pilnikov/WeatherStation/extras/Controllers_sensors/shematic in png/control.png

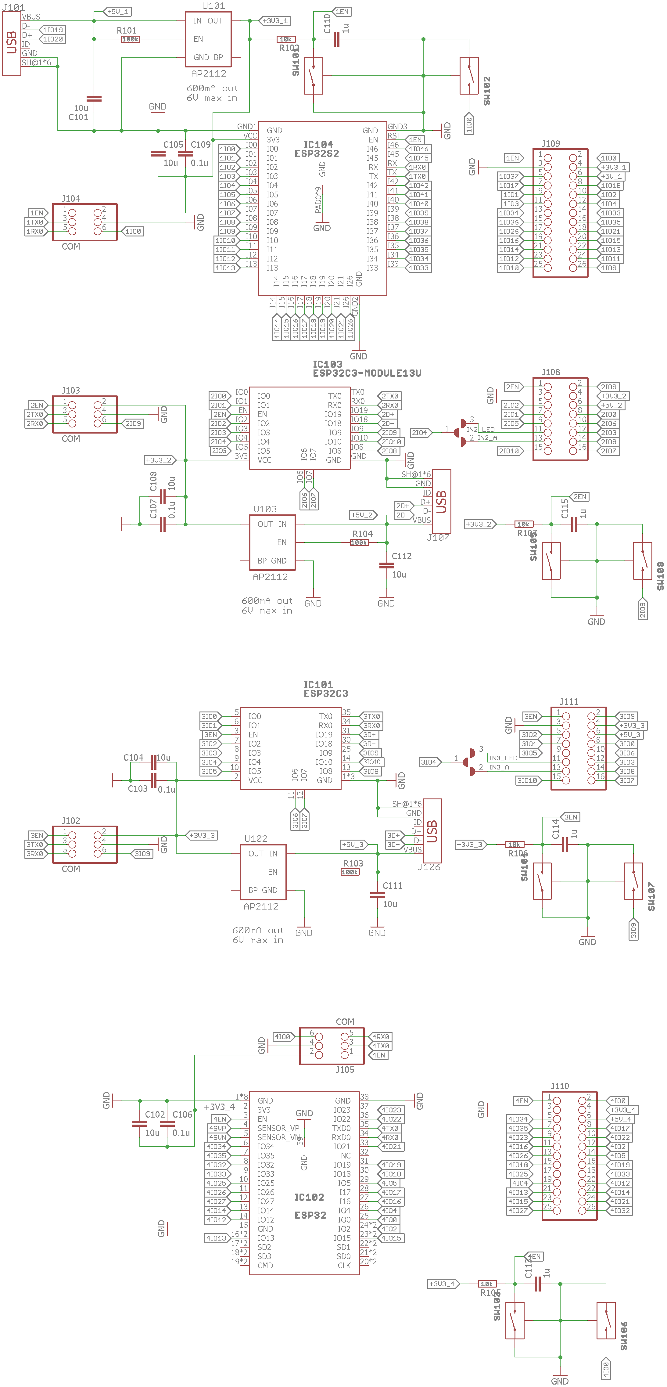
extras/Controllers_sensors/shematic in png/control.png
