pilnikov/WeatherStation/extras/Controllers_sensors/shematic in png/sensor.png

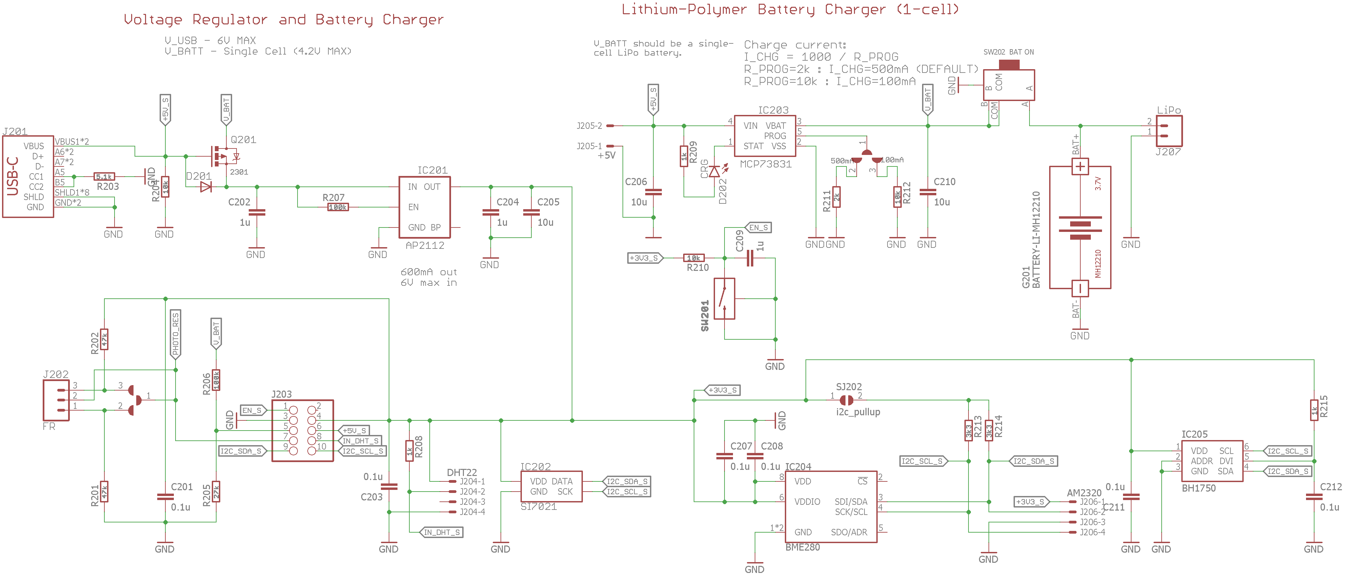
extras/Controllers_sensors/shematic in png/sensor.png
