pilnikov/WeatherStation/extras/Controllers_sensors/shematic in png/usb.png

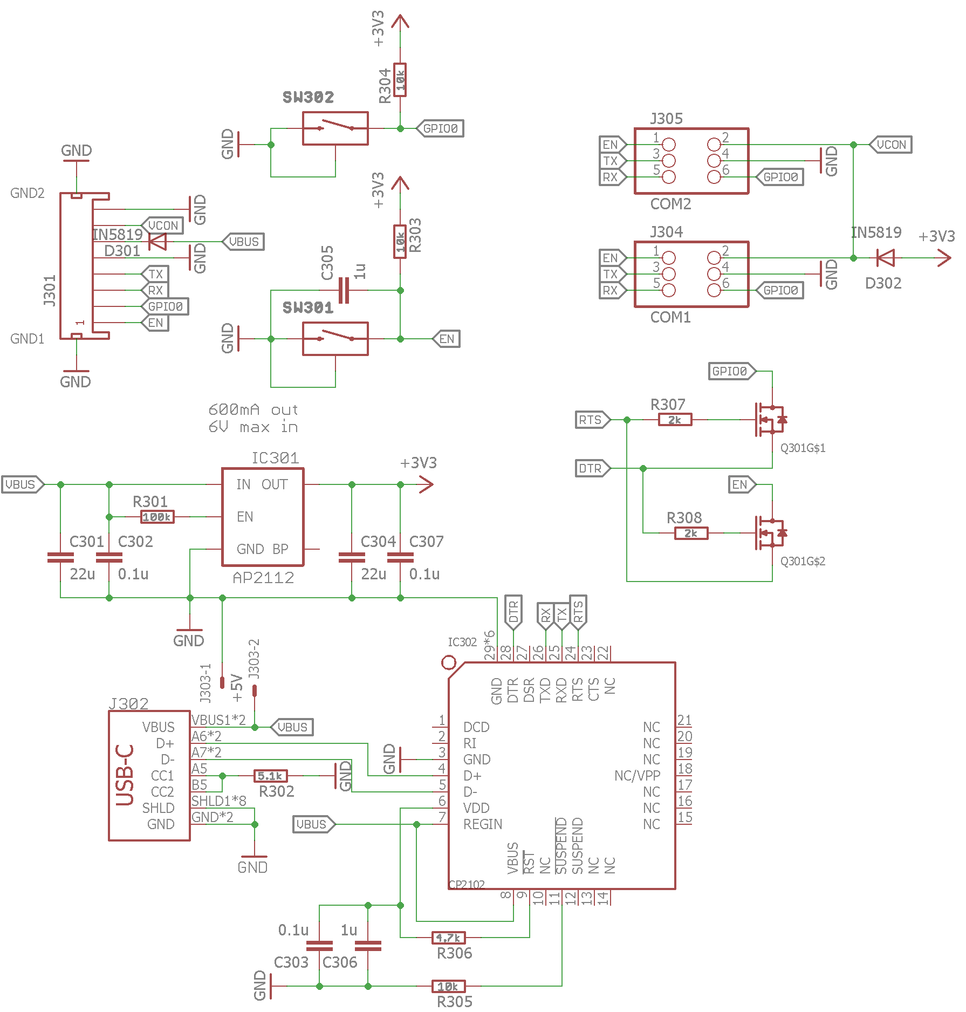
extras/Controllers_sensors/shematic in png/usb.png
