pilnikov/WeatherStation/extras/esp32_hub75/shematic in png/main.png

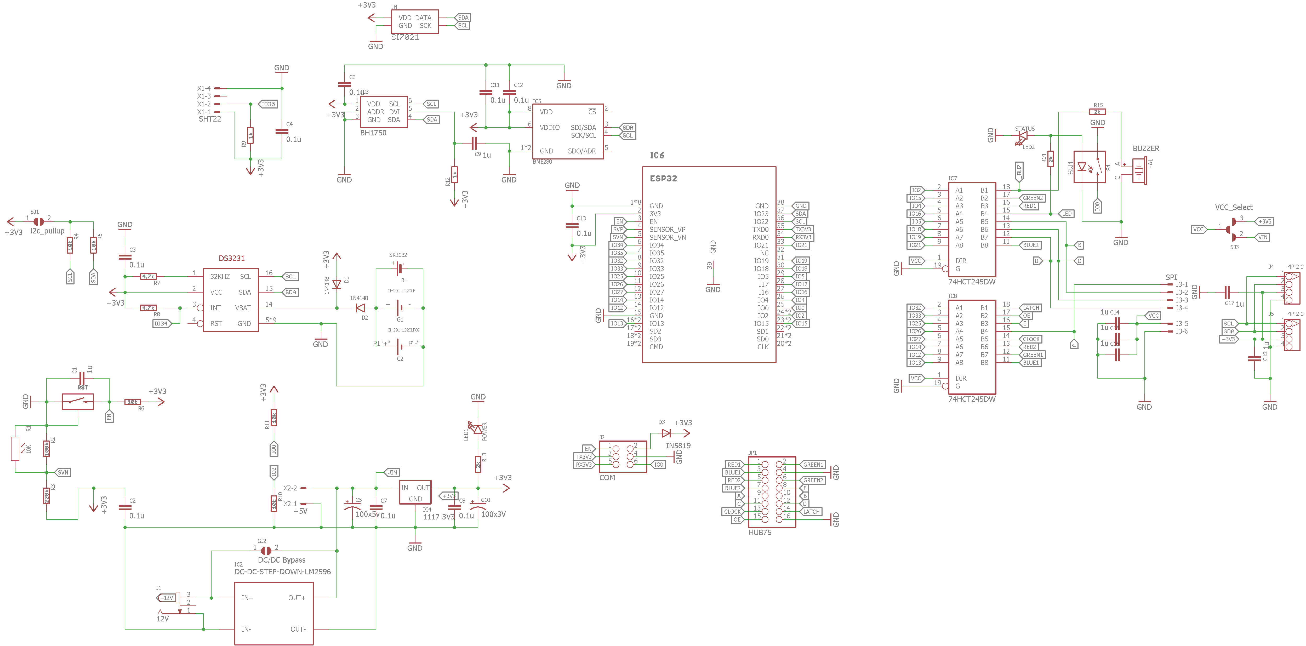
extras/esp32_hub75/shematic in png/main.png
