pilnikov/WeatherStation/extras/Main_board/shematic in png/MAIN.png

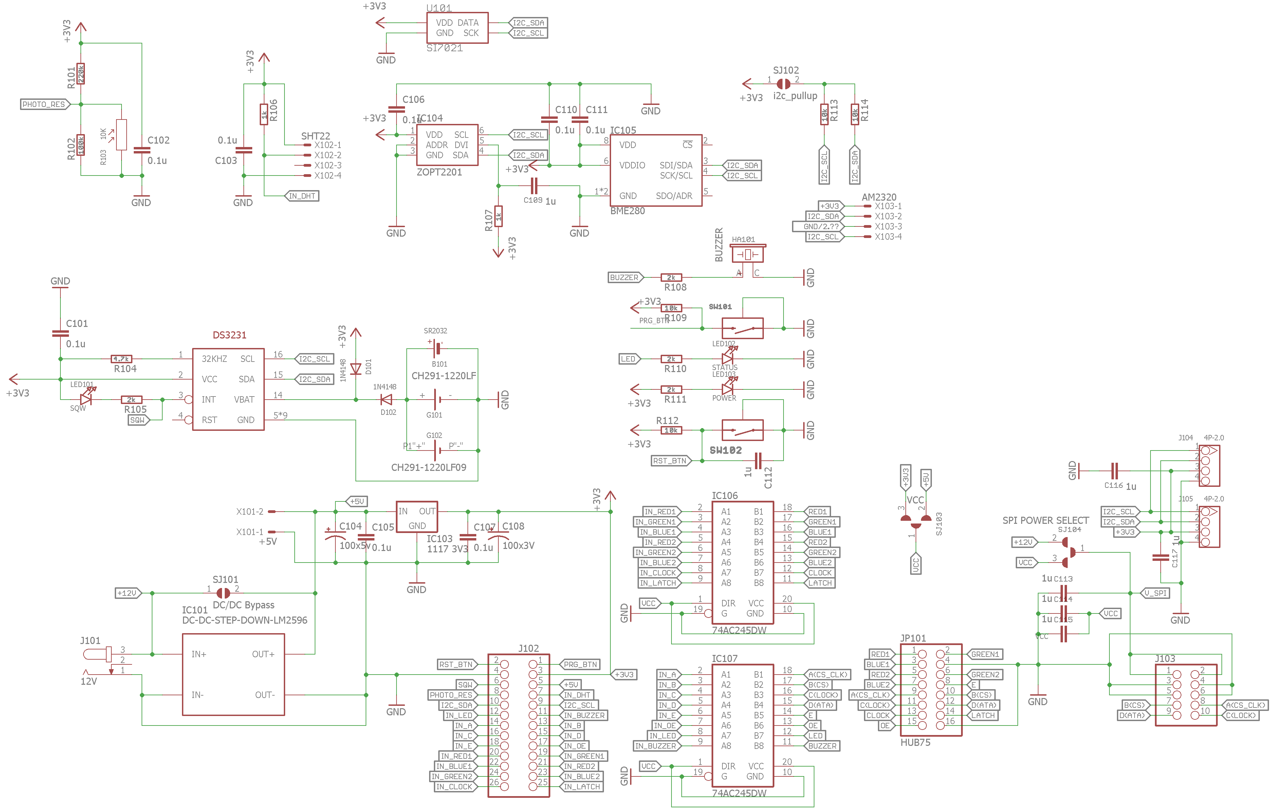
extras/Main_board/shematic in png/MAIN.png
