pilnikov/WeatherStation/extras/Main_board/shematic in png/wifi com.png

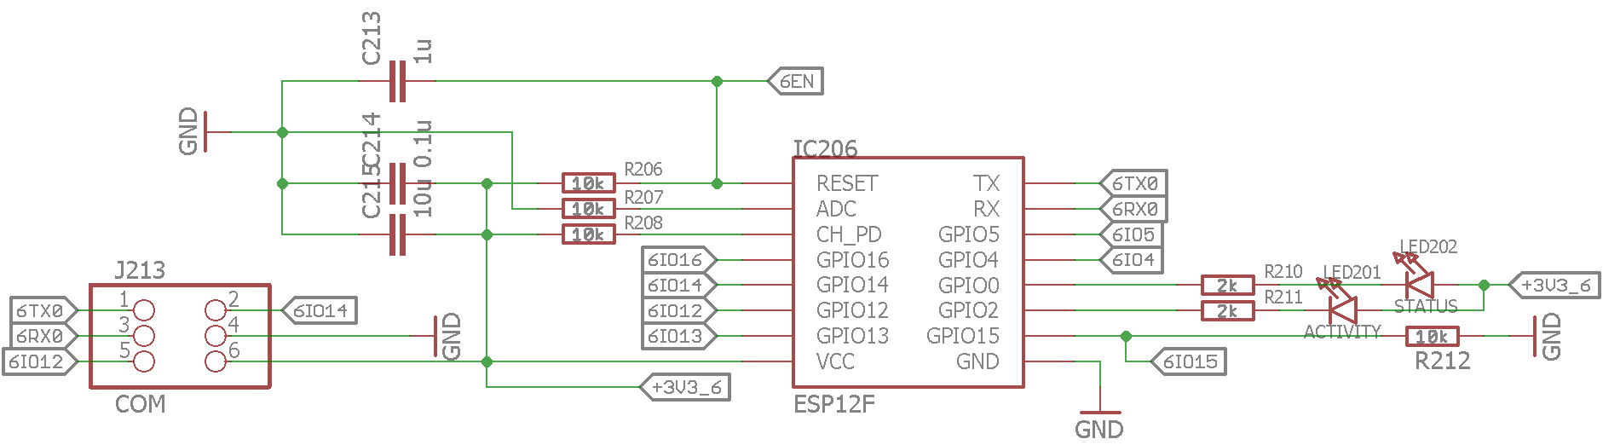
extras/Main_board/shematic in png/wifi com.png
