pilnikov/WeatherStation/extras/max7219_16x32/shematic in png/als318.png

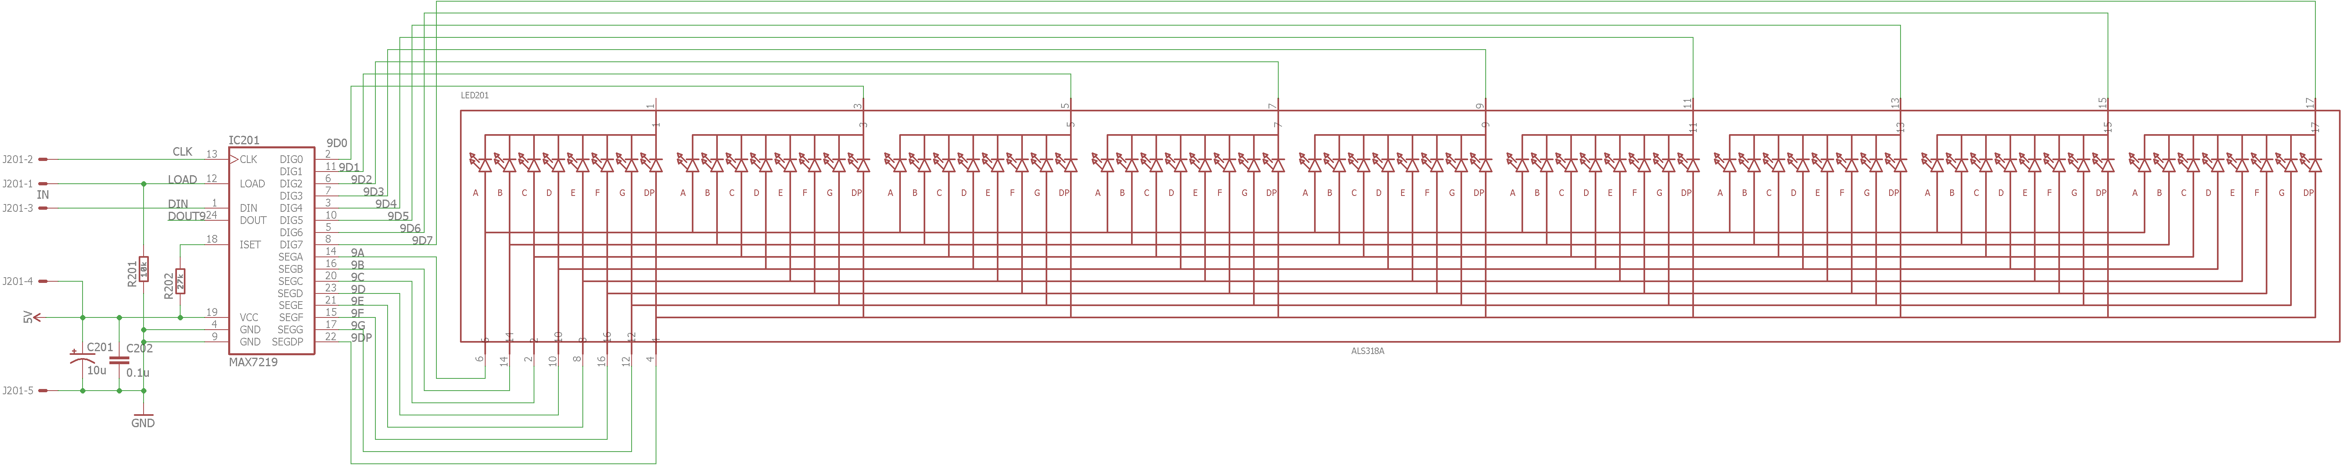
extras/max7219_16x32/shematic in png/als318.png
