pilnikov/WeatherStation/extras/max7219_16x32/shematic in png/main.png

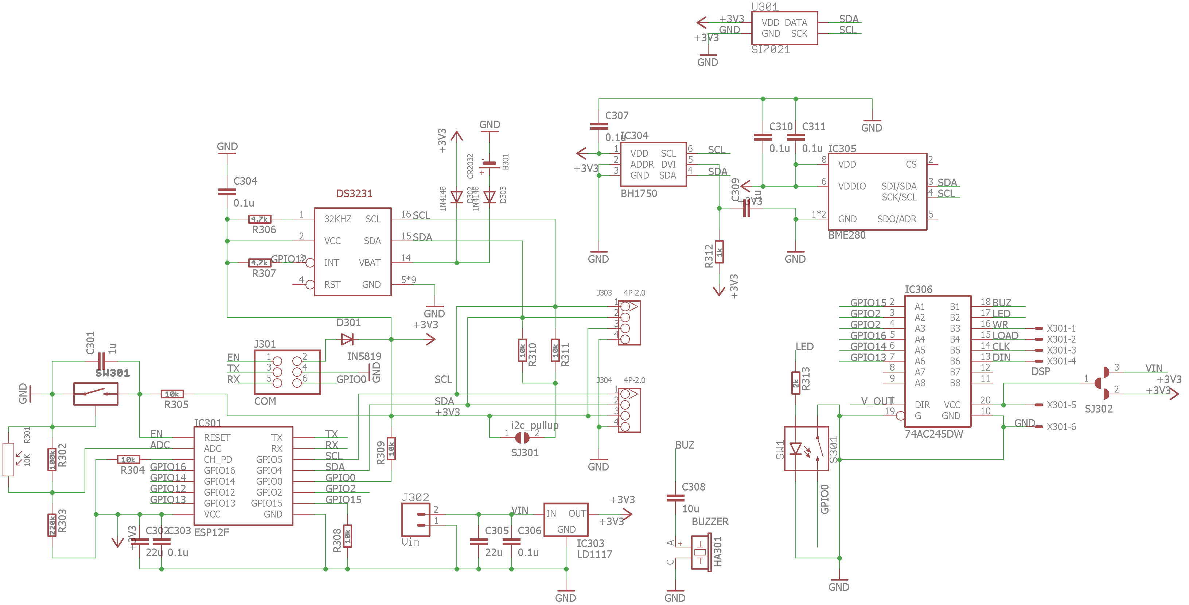
extras/max7219_16x32/shematic in png/main.png
