pilnikov/WeatherStation/extras/max7219_16x32/shematic in png/matrix.png

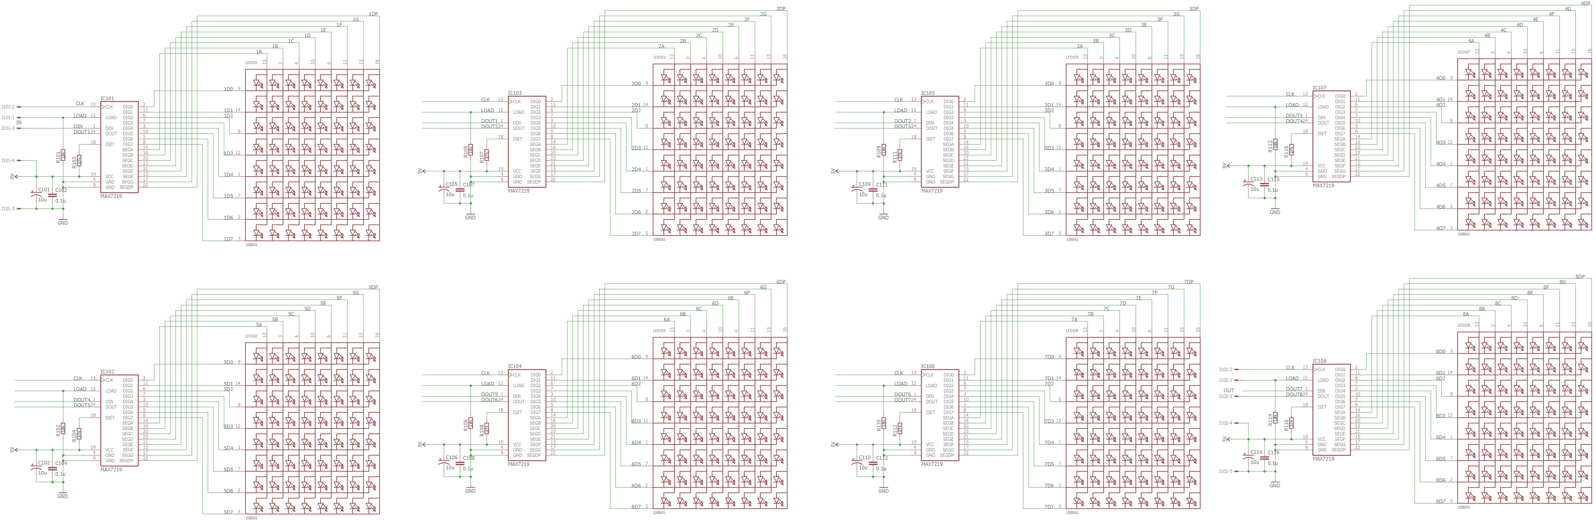
extras/max7219_16x32/shematic in png/matrix.png
