pilnikov/WeatherStation/extras/max7219_16x32/shematic in png/usb.png

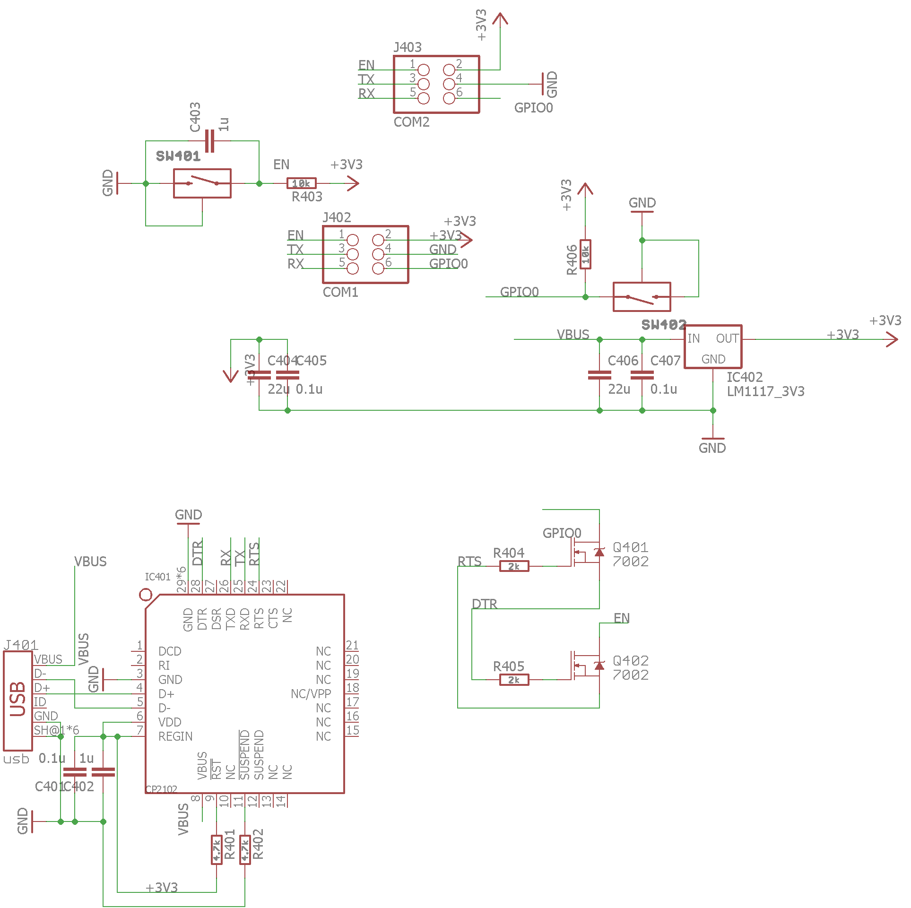
extras/max7219_16x32/shematic in png/usb.png
