pilnikov/WeatherStation/Tablo/connect.PNG

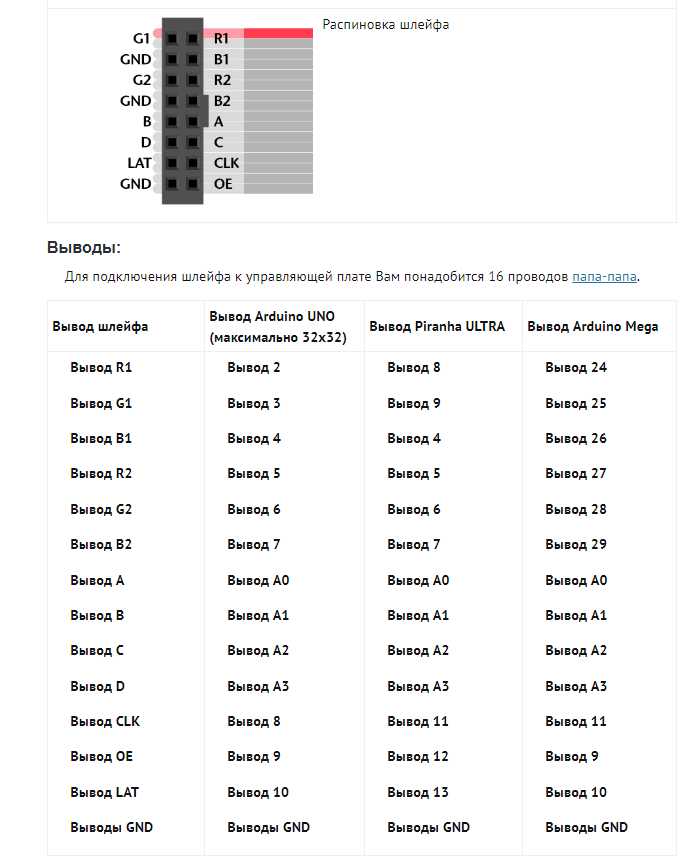
Tablo/connect.PNG
