pilnikov/WeatherStation/wc_rt1/images/edit.JPG

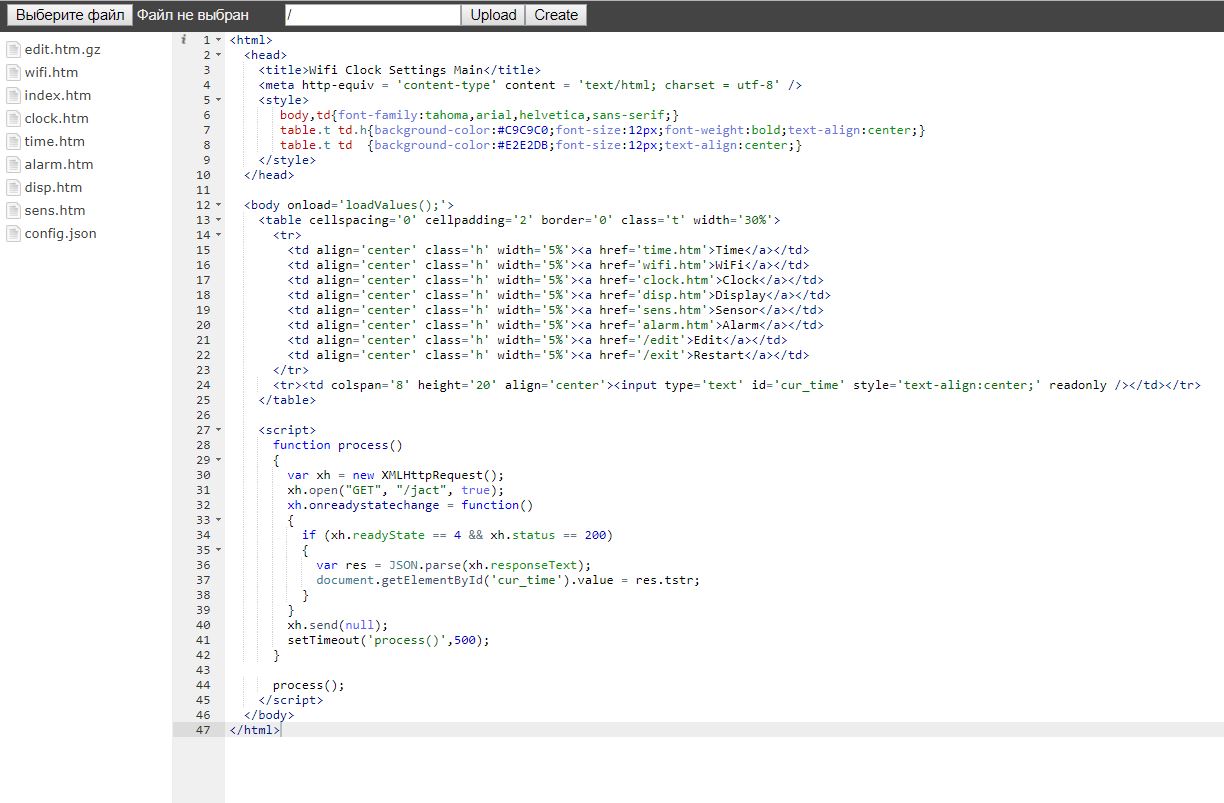
wc_rt1/images/edit.JPG
