pilnikov/WeatherStation/wc_rt1/images/index.jpg

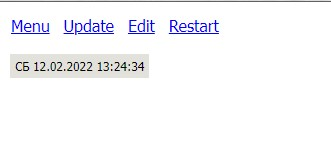
wc_rt1/images/index.jpg
