pilnikov/WeatherStation/wc_rt1/images/news.JPG

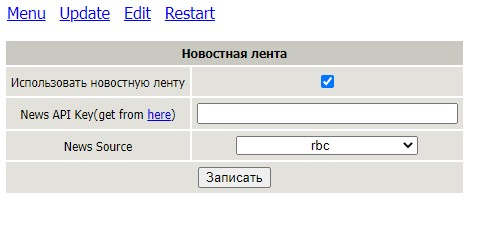
wc_rt1/images/news.JPG
