pilnikov/WeatherStation/wc_rt1/images/sens.JPG

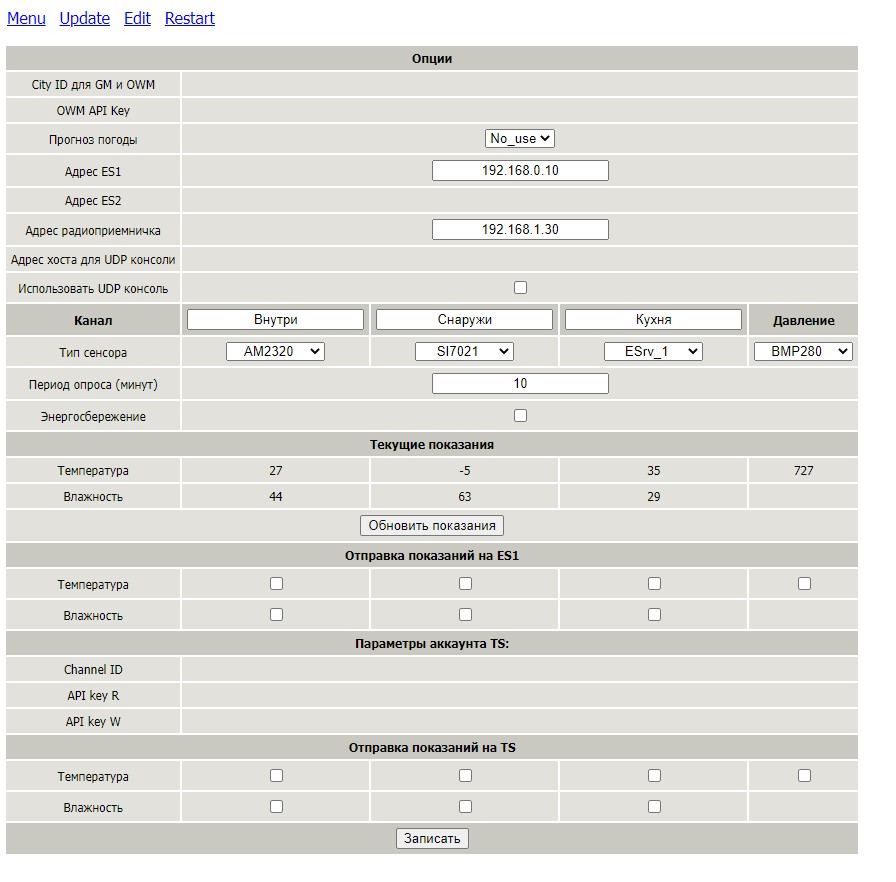
wc_rt1/images/sens.JPG
