pilnikov/WeatherStation/wc_rt1/images/thermo.JPG

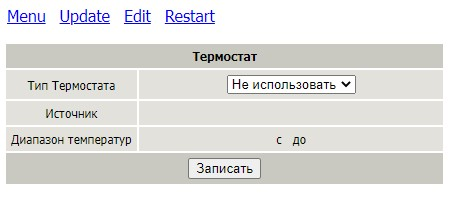
wc_rt1/images/thermo.JPG
