pilnikov/WeatherStation/wc_rt1/images/time.JPG

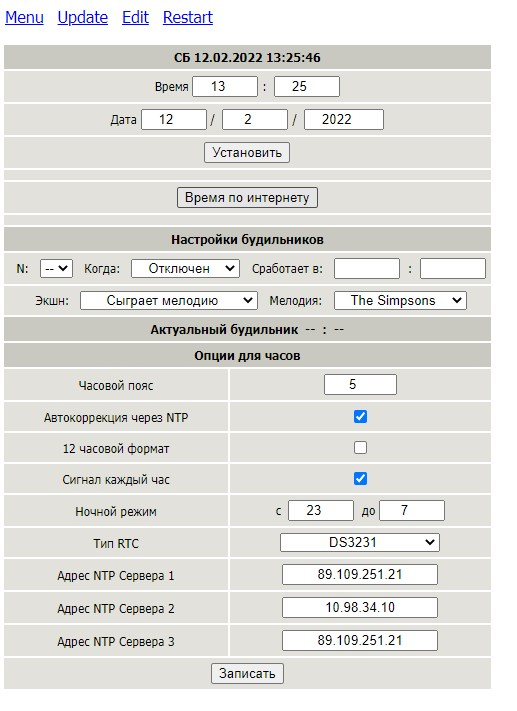
wc_rt1/images/time.JPG
