pilnikov/WeatherStation/wc_rt1/images/wifi.JPG

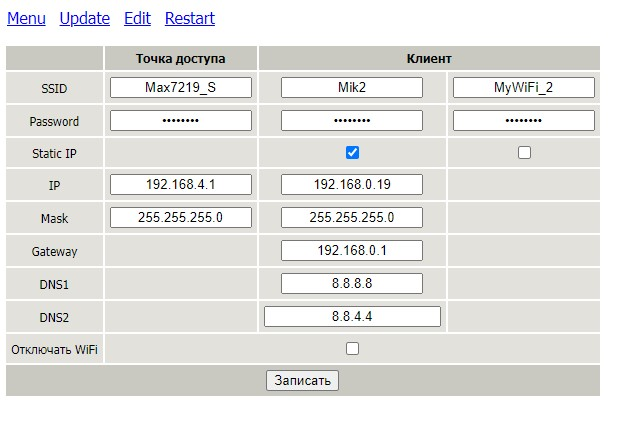
wc_rt1/images/wifi.JPG
