pilnikov/WeatherStation/meteo_gps/conf.h

/*

 * **************Common*********************

*/

#include <TimeLib.h>

/*
 * **************RTC*********************

*/
#include <Wire.h> // must be included here so that Arduino library object file references work
#include <RtcDS3231.h>
RtcDS3231<TwoWire> Rtc(Wire);

unsigned long t_start = millis(), t_dsec = millis(), irq_end[2];
bool colon;
uint8_t disp_mode;

bool si7021_present = false, //SI7021 is present
     am2320_present = false, //AM2320 is present
     bmp180_present = false, //BMP180 is present
     bmp280_present = false, //BMP280 is present
     bme280_present = false, //BME280 is present
     bh1750_present = false, //BH1750 is present
     ds3231_present = true;  //DS3231 is present

int sh[3] = {0, 0, 0}, st[3] = { -99, -99, -99}, p1 = 700;

typedef struct
{
  byte dig[4];
} scr_buff_t;

typedef struct
{
  float t = -99, h = -99, p = 700 ;
} snr_para_t;

typedef struct
{
  uint8_t ch[3];
} snr_ch_t;

snr_ch_t sens = {3, 5, 9};




/*

 * ******************* Sensor*********************

*/

#include <Adafruit_Sensor.h>
#include <Adafruit_HTU21DF.h>
#include <Adafruit_BMP280.h>
#include <Adafruit_BME280.h>
#include <DHT.h>
#include <DHT_U.h>

#define SEALEVELPRESSURE_HPA (1013.25)


//----------------------------------------------------------dht


#define DHTPIN            6         // Pin which is connected to the DHT sensor.

// Uncomment the type of sensor in use:
//#define DHTTYPE           DHT11     // DHT 11
#define DHTTYPE           DHT22     // DHT 22 (AM2302)
//#define DHTTYPE           DHT21     // DHT 21 (AM2301)

// See guide for details on sensor wiring and usage:
//   https://learn.adafruit.com/dht/overview

DHT_Unified dht(DHTPIN, DHTTYPE);

uint32_t delayMS;

//----------------------------------------------------------htu
Adafruit_HTU21DF sht = Adafruit_HTU21DF();

//----------------------------------------------------------bmp2
Adafruit_BMP280 bmp2; // I2C

//----------------------------------------------------------bme

Adafruit_BME280 bme; // I2C

snr_para_t sht_read();
snr_para_t bmp280_read();
snr_para_t bme280_read();
void  dht_init();
snr_para_t dht_read();


snr_ch_t snr_init(snr_ch_t);
void read_snr(snr_ch_t);


/*
 * ***************************display****************************
*/
const byte charArray[] PROGMEM = {
  //GFEDCBA  Segments      7-segment map:
  0b0111111, // 0   "0"          AAA
  0b0000110, // 1   "1"         F   B
  0b1011011, // 2   "2"         F   B
  0b1001111, // 3   "3"          GGG
  0b1100110, // 4   "4"         E   C
  0b1101101, // 5   "5"         E   C
  0b1111101, // 6   "6"          DDD
  0b0000111, // 7   "7"
  0b1111111, // 8   "8"
  0b1101111, // 9   "9"
  0b1110111, // 10  "A"
  0b1111100, // 11  "b"
  0b0111001, // 12  "C"
  0b1011110, // 13  "d"
  0b1111001, // 14  "E"
  0b1110001, // 15  "F"
  0b0000000, // 16  NO DISPLAY
  0b0000000, // 17  NO DISPLAY
  0b0000000, // 18  NO DISPLAY
  0b0000000, // 19  NO DISPLAY
  0b0000000, // 20  NO DISPLAY
  0b0000000, // 21  NO DISPLAY
  0b0000000, // 22  NO DISPLAY
  0b0000000, // 23  NO DISPLAY
  0b0000000, // 24  NO DISPLAY
  0b0000000, // 25  NO DISPLAY
  0b0000000, // 26  NO DISPLAY
  0b0000000, // 27  NO DISPLAY
  0b0000000, // 28  NO DISPLAY
  0b0000000, // 29  NO DISPLAY
  0b0000000, // 30  NO DISPLAY
  0b0000000, // 31  NO DISPLAY
  0b0000000, // 32  ' '
  0b0000000, // 33  '!'  NO DISPLAY
  0b0100010, // 34  '"'
  0b0000000, // 35  '#'  NO DISPLAY
  0b0000000, // 36  '$'  NO DISPLAY
  0b0000000, // 37  '%'  NO DISPLAY
  0b0000000, // 38  '&'  NO DISPLAY
  0b0000010, // 39  '''
  0b0111001, // 40  '('
  0b0001111, // 41  ')'
  0b0000000, // 42  '*'  NO DISPLAY
  0b0000000, // 43  '+'  NO DISPLAY
  0b0010000, // 44  ','
  0b1000000, // 45  '-'
  0b10000000,// 46  '.'
  0b0000000, // 47  '/'  NO DISPLAY
  0b0111111, // 48  "0"
  0b0000110, // 49  "1"
  0b1011011, // 50  "2"
  0b1001111, // 51  "3"
  0b1100110, // 52  "4"
  0b1101101, // 53  "5"
  0b1111101, // 54  "6"
  0b0000111, // 55  "7"
  0b1111111, // 56  "8"
  0b1101111, // 57  "9"
  0b1000001, // 58  ':'  NO DISPLAY
  0b1001000, // 59  ';'  NO DISPLAY
  0b1000110, // 60  '<'  NO DISPLAY
  0b0000000, // 61  '='  NO DISPLAY
  0b1110000, // 62  '>'  NO DISPLAY
  0b0000000, // 63  '?'  NO DISPLAY
  0b0000000, // 64  '@'  NO DISPLAY
  0b1110111, // 65  "A"
  0b1111100, // 66  "b"
  0b0111001, // 67  "C"
  0b1011110, // 68  "d"
  0b1111001, // 69  "E"
  0b1110001, // 70  "F"
  0b1101111, // 71  'G'
  0b1110110, // 72  'H'
  0b0000110, // 73  'I'
  0b0011110, // 74  'J'
  0b1110110, // 75  'K'  NO DISPLAY
  0b0111000, // 76  'L'
  0b0010101, // 77  'M'  NO DISPLAY
  0b1010100, // 78  'n'
  0b0111111, // 79  'O'
  0b1110011, // 80  'P'
  0b1100111, // 81  'q'
  0b1010000, // 82  'r'
  0b1101101, // 83  'S'
  0b1111000, // 84  't'
  0b0111110, // 85  'U'
  0b0011100, // 86  'V'  NO DISPLAY
  0b0101010, // 87  'W'  NO DISPLAY
  0b1110110, // 88  'X'  NO DISPLAY
  0b1101110, // 89  'y'
  0b1011011, // 90  'Z'  NO DISPLAY
  0b0111001, // 91  '['
  0b0000000, // 92  '\'  NO DISPLAY
  0b0001111, // 93  ']'
  0b0000001, // 94  '^'  NO DISPLAY
  0b0001000, // 95  '_'
  0b0000010, // 96  '`'
  0b1110111, // 97  'a' SAME AS CAP
  0b1111100, // 98  'b' SAME AS CAP
  0b1011000, // 99  'c'
  0b1011110, // 100 'd' SAME AS CAP
  0b1111011, // 101 'e'
  0b1110001, // 102 'F' SAME AS CAP
  0b0111101, // 103 'G' SAME AS CAP
  0b1110100, // 104 'h'
  0b0000100, // 105 'i'
  0b0011110, // 106 'j' SAME AS CAP
  0b0000000, // 107 'k'  NO DISPLAY
  0b0000110, // 108 'l'
  0b0000000, // 109 'm'  NO DISPLAY
  0b1010100, // 110 'n' SAME AS CAP
  0b1011100, // 111 'o'
  0b1110011, // 112 'p' SAME AS CAP
  0b1100111, // 113 'q' SAME AS CAP
  0b1010000, // 114 'r' SAME AS CAP
  0b1101101, // 115 'S' SAME AS CAP
  0b1111000, // 116 't' SAME AS CAP
  0b0011100, // 117 'u'
  0b0000000, // 118 'b'  NO DISPLAY
  0b0000000, // 119 'w'  NO DISPLAY
  0b0000000, // 120 'x'  NO DISPLAY
  0b0000000, // 121 'y'  NO DISPLAY
  0b0000000, // 122 'z'  NO DISPLAY
  0b0000000, // 123 '0b' NO DISPLAY
  0b0000000, // 124 '|'  NO DISPLAY
  0b0000000, // 125 ','  NO DISPLAY
  0b0000000, // 126 '~'  NO DISPLAY
  0b0000000, // 127 'DEL'  NO DISPLAY
  0b0000000, // 128 NO DISPLAY
  0b0000000, // 129 NO DISPLAY
  0b0000000, // 130 NO DISPLAY
  0b0000000, // 131 NO DISPLAY
  0b0000000, // 132 NO DISPLAY
  0b0000000, // 133 NO DISPLAY
  0b0000000, // 134 NO DISPLAY
  0b0000000, // 135 NO DISPLAY
  0b0000000, // 136 NO DISPLAY
  0b0000000, // 137 NO DISPLAY
  0b0000000, // 138 NO DISPLAY
  0b0000000, // 139 NO DISPLAY
  0b0000000, // 140 NO DISPLAY
  0b0000000, // 141 NO DISPLAY
  0b0000000, // 142 NO DISPLAY
  0b0000000, // 143 NO DISPLAY
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
  0b0000000, // 255 'я'  NO DISPLAY
};


#include <TM1637.h>

#define CLK 5//pins definitions for TM1637 and can be changed to other ports
#define DIO 4

TM1637 tm1637(CLK, DIO);

int8_t TimeDisp[] = {0xff, 0xff, 0xff, 0xff};
scr_buff_t s7dig;                               // разряды индикаторов
