pilnikov/WeatherStation/sound/sound_utro.ino

void utro() {
#if !defined(ARDUINO_ARCH_ESP32)
  tone(BUZ_PIN, 700, 300);
  delay(600);
  tone(BUZ_PIN, 700, 300);
  delay(600);
  tone(BUZ_PIN, 780, 150);
  delay(300);
  tone(BUZ_PIN, 700, 150);
  delay(300);
  tone(BUZ_PIN, 625, 450);
  delay(600);
  tone(BUZ_PIN, 590, 150);
  delay(300);
  tone(BUZ_PIN, 520, 150);
  delay(300);
  tone(BUZ_PIN, 460, 450);
  delay(600);
  tone(BUZ_PIN, 350, 450);
  delay(600);
  delay(600);
  tone(BUZ_PIN, 350, 450);
  delay(600);
  tone(BUZ_PIN, 460, 450);
  delay(600);
  tone(BUZ_PIN, 520, 150);
  delay(300);
  tone(BUZ_PIN, 590, 150);
  delay(300);
  tone(BUZ_PIN, 625, 450);
  delay(600);
  tone(BUZ_PIN, 590, 150);
  delay(300);
  tone(BUZ_PIN, 520, 150);
  delay(300);
  tone(BUZ_PIN, 700, 1350);
  delay(1800);
  tone(BUZ_PIN, 700, 300);
  delay(600);
  tone(BUZ_PIN, 700, 300);
  delay(600);
  tone(BUZ_PIN, 780, 150);
  delay(300);
  tone(BUZ_PIN, 700, 150);
  delay(300);
  tone(BUZ_PIN, 625, 450);
  delay(600);
  tone(BUZ_PIN, 590, 150);
  delay(300);
  tone(BUZ_PIN, 520, 150);
  delay(300);
  tone(BUZ_PIN, 460, 450);
  delay(600);
  tone(BUZ_PIN, 350, 450);
  delay(600);
  delay(600);
  tone(BUZ_PIN, 350, 450);
  delay(600);
  tone(BUZ_PIN, 625, 450);
  delay(600);
  tone(BUZ_PIN, 590, 150);
  delay(300);
  tone(BUZ_PIN, 520, 150);
  delay(300);
  tone(BUZ_PIN, 700, 450);
  delay(600);
  tone(BUZ_PIN, 590, 150);
  delay(300);
  tone(BUZ_PIN, 520, 150);
  delay(300);
  tone(BUZ_PIN, 460, 1350);
  delay(5000);
#endif
}
