pilnikov/WeatherStation/Tablo/Header.h

// testshapes demo for RGBm3216Panel library.
// Demonstrates the drawing abilities of the RGBm3216Panel library.
// For 32x64 RGB LED m3216.

// NOTE THIS CAN ONLY BE USED ON A MEGA! NOT ENOUGH RAM ON UNO!

#include <ArduinoJson.h>
#include <RtcDS3231.h>
#include <EEPROM.h>
#include <Wire.h>
#include <BH1750.h>

#include "Songs.h"
#include "fonts.h"
#include "rtc.h"

#include <Snd.h>
#include <Udt.h>
#include <Sysf2.h>
#include <Snr.h>
#include <Fdsp.h>


void synchro();
String Serial_Read();

void parser(String);

void m3216_init();
void pr_str(uint8_t&, uint8_t, conf_data_t, snr_data_t, wf_data_t, wf_data_t, rtc_data_t, String, uint8_t, char*);

#ifndef DBG_OUT_PORT
#define DBG_OUT_PORT Serial
#endif


//---------------------------------------------------------------------------Matrix
#if   defined(__AVR_ATmega2560__)
#include <RGBmatrixPanel.h> // Hardware-specific library
static RGBmatrixPanel * m3216;
#elif defined(ARDUINO_ARCH_ESP32)
#include <Adafruit_Protomatter.h>
static Adafruit_Protomatter * m3216;
#endif


//-------------------------------------------------------Sensor
static SNR sens;

//--------------------------------------------------- Common

static SF fsys;
static FD f_dsp;

static BH1750 lightMeter;

static Synt Buzz;               //Конструктор пищалки

snr_data_t snr_data;
wf_data_t wf_data;
wf_data_t wf_data_cur;
snr_data_t es_data1;

conf_data_t conf_data;
ram_data_t ram_data;

rtc_data_t rtc_data;


//-------------------------------------------------------m3216

const uint8_t q_dig = 6;  // количество цифр на дисплее

static uint8_t cur_sym_pos[3] = {0, 0, 0};
static uint16_t buffud[64];
static bool d_notequal[q_dig];
const uint8_t digPos_x[q_dig] = {0, 6, 13, 19, 25, 29}; // позиции цифр на экране по оси x
static unsigned char oldDigit[q_dig];                       // убегающая цифра
static uint8_t  num_st = 1;
uint8_t max_st = 5; //номер и макс кол-во прокручиваемых строк
uint8_t  text_size = 1;   // размер текста

static char st1[254];
 
byte screen[64]; // display buffer

bool play_snd = false, nm_is_on = false, disp_on = true, end_run_st = false;

uint8_t cur_br = 255, debug_level = 0;
