pilnikov/WeatherStation/Test_rtc/Test_rtc.ino

/////////////////////////////////////////////////////////////////////////////////////////
//#include ".\headers\conf.h"
#include "conf.h"

void setup()
{
  //------------------------------------------------------  Определяем консоль
  DBG_OUT_PORT.begin(115200);
  DBG_OUT_PORT.println(F("Test RTC"));

#if defined(__xtensa__) || CONFIG_IDF_TARGET_ESP32C3
  //------------------------------------------------------  Запускаем LittleFileSystem
  lfs.begin();
  DBG_OUT_PORT.println(F("LittleFS started"));

  //------------------------------------------------------  Загружаем конфигурацию

  //------------------------------------------------------  Читаем установки WiFi из конфиг файла
  conf_f = "/conf_wifi.json";
  from_client = lfs.readFile(conf_f);
  wifi_data = wifi_cfg.from_json(from_client);

  //wifi_data = wifi_cfg.def_conf();
  DBG_OUT_PORT.print(conf_f);
  DBG_OUT_PORT.println(F(" loaded"));

  //--------------------------------------------------------  Запускаем основные сетевые сервисы
  //--------------------------------------------------------  Запускаем WiFi
  wifi_data_cur = wifi.begin(wifi_data);

  if (wifi_data_cur.cli || wifi_data_cur.ap)
  {
    //------------------------------------------------------  Запускаем сервер, ОТА, MDNS
    ArduinoOTA.setHostname(wifi_data.ap_ssid);

    // Authentication
    ArduinoOTA.setPassword(wifi_data.ap_pass);

    ArduinoOTA.begin();
    DBG_OUT_PORT.println("OTA Ready");
    DBG_OUT_PORT.print("IP address: ");
    DBG_OUT_PORT.println(WiFi.localIP());

    MDNS.begin(wifi_data.ap_ssid);
    DBG_OUT_PORT.print(F("Open http://"));
    DBG_OUT_PORT.print(wifi_data.ap_ssid);
    DBG_OUT_PORT.print(F(".local/edit to see the file browser\n"));

    web_setup();
    start_serv();
  }
  strcpy(tstr, "Safe Mode");
#endif

#if defined(__xtensa__) || CONFIG_IDF_TARGET_ESP32C3
  //------------------------------------------------------  Читаем установки RTC из конфиг файла
  conf_f = "/conf_rtc.json";
  from_client = lfs.readFile(conf_f);
  rtc_cfg = myrtccfg.from_json(from_client);

  //rtc_cfg = myrtccfg.def_conf();
  DBG_OUT_PORT.print(conf_f);
  DBG_OUT_PORT.println(F(" loaded"));
#endif

  //------------------------------------------------------  GPIO
#if defined(ESP8266)
  rtc_hw.gpio_dio = 13;
  rtc_hw.gpio_clk = 14;
  rtc_hw.gpio_dcs = 16;
  rtc_hw.gpio_sqw = 12;
  gpio_sda = 4;
  gpio_scl = 5;
  gpio_snd = 15;

#elif CONFIG_IDF_TARGET_ESP32
  rtc_hw.gpio_dio = 19;
  rtc_hw.gpio_clk = 18;
  rtc_hw.gpio_dcs = 5;
  rtc_hw.gpio_sqw = 34;
  gpio_sda = 23;
  gpio_scl = 22;
  gpio_snd = 2;
#endif
  //------------------------------------------------------  ТИП МС RTC
  rtc_hw.a_type = rtc_cfg.c_type;

  //------------------------------------------------------  Начинаем инициализацию Hardware
#if CONFIG_IDF_TARGET_ESP32 || CONFIG_IDF_TARGET_ESP32S2 || CONFIG_IDF_TARGET_ESP32C3
  Wire.setPins(gpio_sda, gpio_scl);
# endif
  if (rtc_hw.a_type > 0)
  {
# if defined(ESP8266)
    Wire.begin(gpio_sda, gpio_scl);
# else
    Wire.begin();
# endif
  }

  //ram_data = fsys.i2c_scan(rtc_cfg);
  //------------------------------------------------------  Инициализируем RTC
  if (rtc_hw.a_type > 0) myrtc.rtc_init(rtc_hw);
  DBG_OUT_PORT.print(F("Type of rtc = "));
  DBG_OUT_PORT.println(rtc_hw.a_type);

  RtcDateTime compileDateTime(__DATE__, __TIME__);
  uint32_t ttm = compileDateTime.Epoch32Time();
#if defined(__xtensa__) || CONFIG_IDF_TARGET_ESP32C3
  ttm = myrtc.GetNtp(rtc_cfg, ttm);
#endif
  myrtc.man_set_time(rtc_hw, ttm);
  rtc_time.ct = myrtc.GetTime(rtc_hw);
  rtc_alm = myrtc.set_alarm(rtc_cfg, rtc_time.ct, rtc_hw.a_type == 1);


  //------------------------------------------------------ Радостно пищим по окончаниии подготовки к запуску
  rtc_alm.act = 15;
  play_snd = true;
  DBG_OUT_PORT.println(F("End of setup"));

}

void loop()
{
  // ----------------------------------------------------- Проигрываем звуки
  uint8_t muz_n = 15;
  if  (rtc_alm.act < 20)  muz_n = rtc_alm.act;
  Buzz.play(muz_n, gpio_snd, play_snd, false);
  play_snd = false;


  //-------------Refresh current time in rtc_cfg------------------
  rtc_time.ct = myrtc.GetTime(rtc_hw);

  myrtc.cur_time_str(rtc_time, true, tstr);

  if (!wasAlarm) //Проверка будильников
  {
    bool aaaa = !digitalRead(rtc_hw.gpio_sqw);
    if (myrtc.Alarmed(aaaa, rtc_hw, &rtc_alm, rtc_time.ct))
    {
      _wasAlarmed_int = false;
      if (rtc_alm.al1_on) alarm1_action();
      if (rtc_alm.al2_on & !rtc_time.nm_is_on & rtc_cfg.every_hour_beep)
      {
        rtc_alm.act = 15;
        play_snd = true;
      }
      wasAlarm = true;
      alarm_time = millis() + 2000;
    }
  }

  if (wasAlarm & (millis() > alarm_time)) //Перезапуск будильников
  {
    rtc_alm = myrtc.set_alarm(rtc_cfg, rtc_time.ct, rtc_hw.a_type == 1);
    wasAlarm = false;
  }
  //------------------------------------------------------  Верифицируем ночной режим
  rtc_time.nm_is_on = myrtc.nm_act(rtc_time.ct, rtc_cfg.nm_start, rtc_cfg.nm_stop);
#if defined(__xtensa__) || CONFIG_IDF_TARGET_ESP32C3
  server.handleClient();
  ArduinoOTA.handle();
#endif
}
